SolderedElectronics/Simple-fire-sensor-board-with-easyC-hardware-design/OUTPUTS/V1.1.2/Simple fire sensor with easyC.jpg

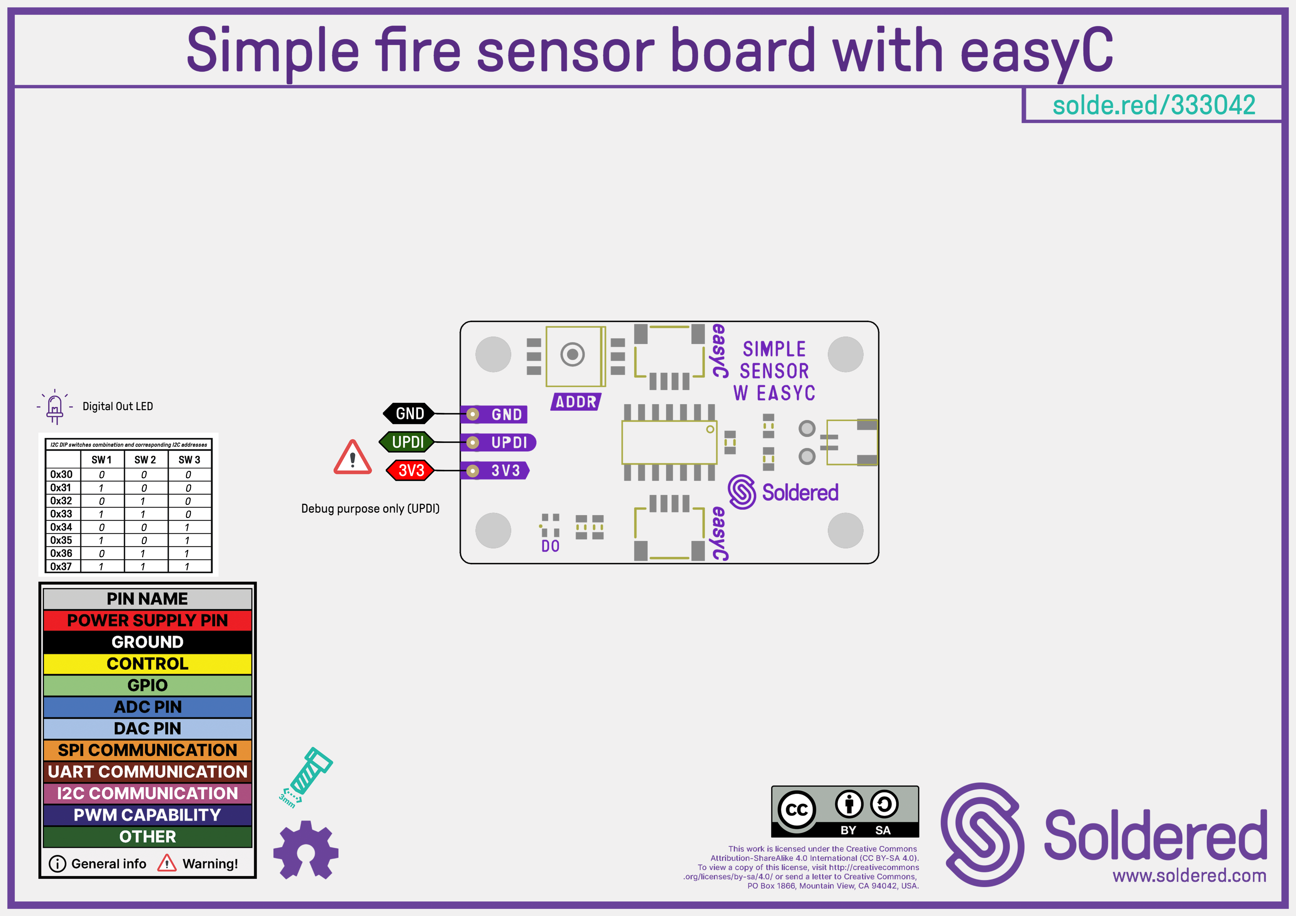
OUTPUTS/V1.1.2/Simple fire sensor with easyC.jpg
